holmesrichards/mults/Docs/Layout/multiples_panel/multiples_panel_B.SilkS.pdf

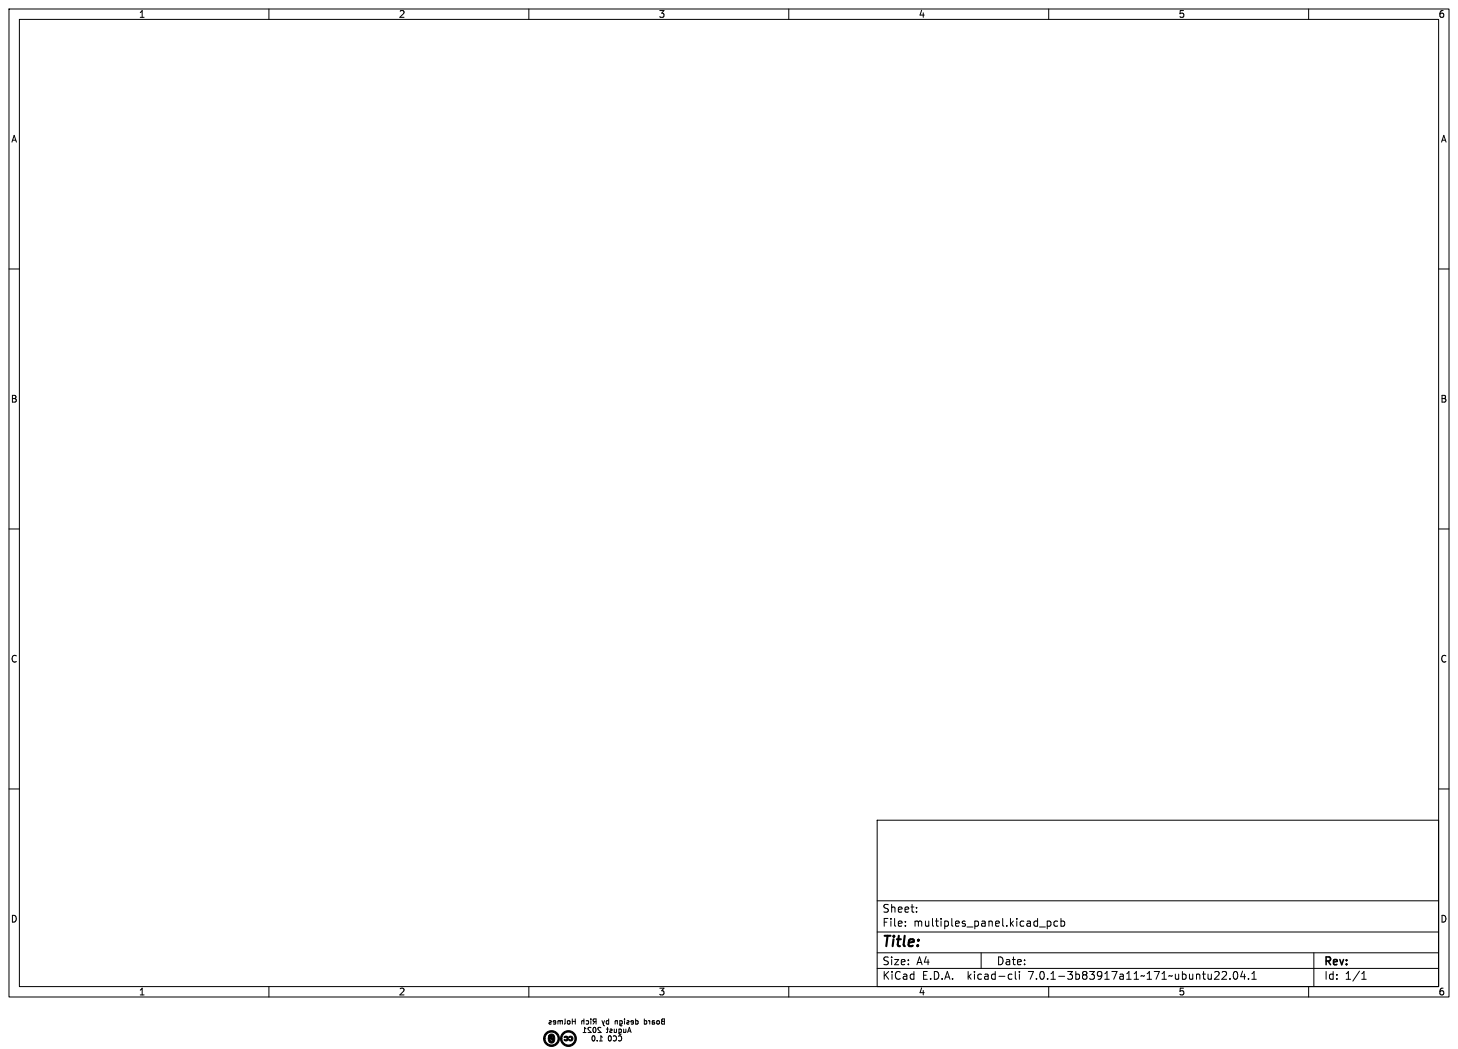
[picture p14: page 1]

Id: 1/1 Title: File: multiples_panel.kicad_pcb Sheet: Board design by Rich Holmes August 2021 CC0 1.0
