holmesrichards/mults/Docs/Layout/multiples_panel/multiples_panel_Edge.Cuts.pdf

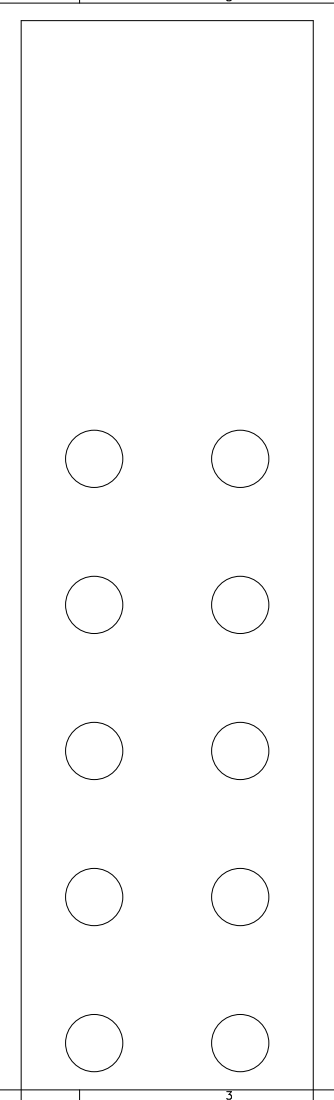
[picture p15: page 1]

Id: 1/1 Title: File: multiples_panel.kicad_pcb Sheet:
