holmesrichards/mults/Docs/Layout/multiples_panel/multiples_panel_F.Cu.pdf

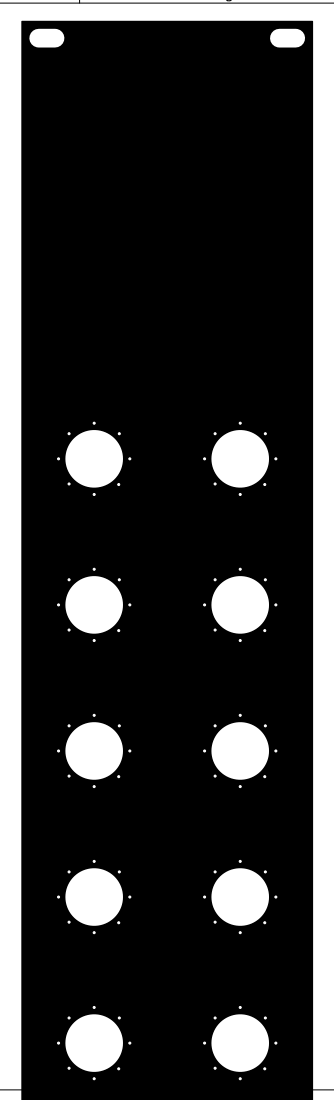
[picture p16: page 1]

Id: 1/1 Title: File: multiples_panel.kicad_pcb Sheet:
