holmesrichards/mults/Docs/Layout/multiples_panel/multiples_panel_F.Mask.pdf

Id: 1/1 Title: File: multiples_panel.kicad_pcb Sheet:
